JeSuisMaksique/Curse/DOCS/Схема структурная.pdf

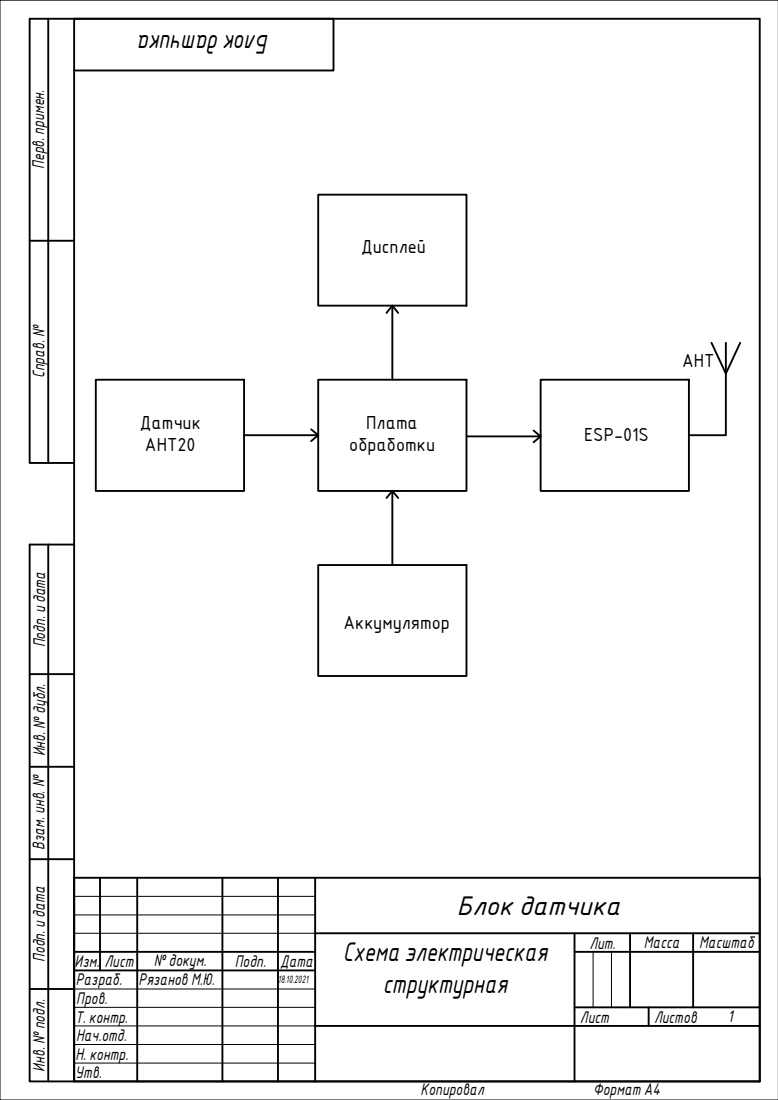
[picture p35: page 1]
Формат A4; Инв. №; л. Под; бл. Под; Перв. п

Блок датчика

Схема электрическая структурная | Лит. | Масса | Масштаб

Изм. | Лист | № докум. | Подп. | Дата
Разраб. | | Рязанов М.Ю. | | 18.10.2021
Пров.
Т. контр. | | | | | Лист | Листов 1
Нач.отд.
Н. контр.
Утв.
